razrotenberg/Arpeggino/tutorial/3__lcd/3_1__multiplexer/3_1__multiplexer.jpg

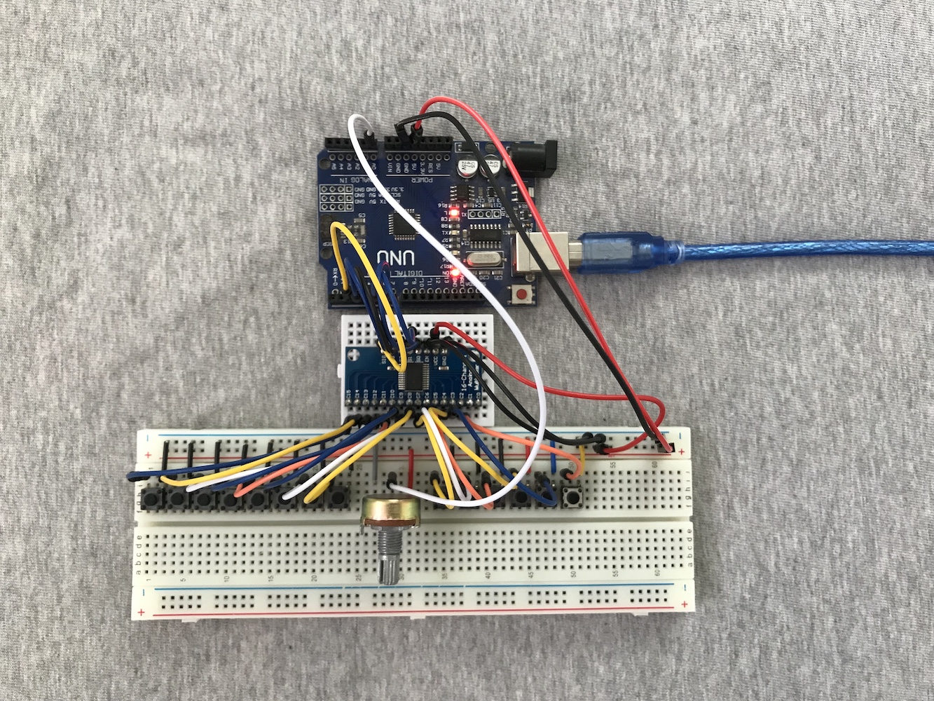
tutorial/3__lcd/3_1__multiplexer/3_1__multiplexer.jpg
