razrotenberg/Arpeggino/tutorial/4__recording/4__recording.jpg

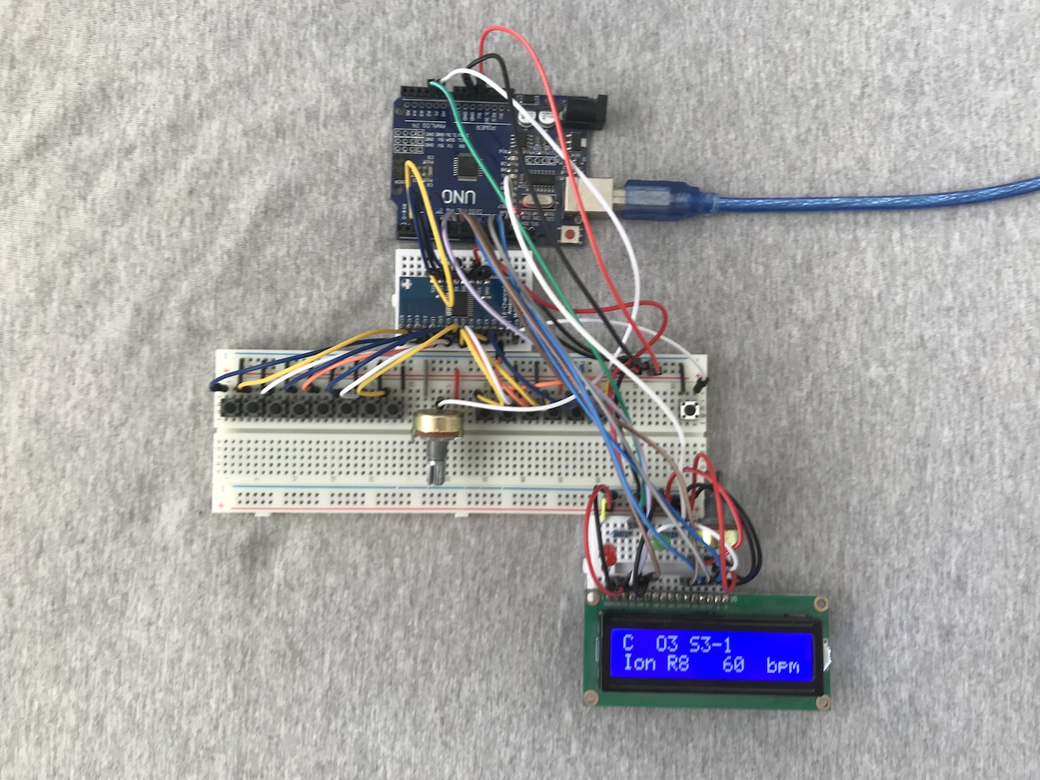
tutorial/4__recording/4__recording.jpg
